hack-apollo/hack_clock/hardware/images/2.jpg

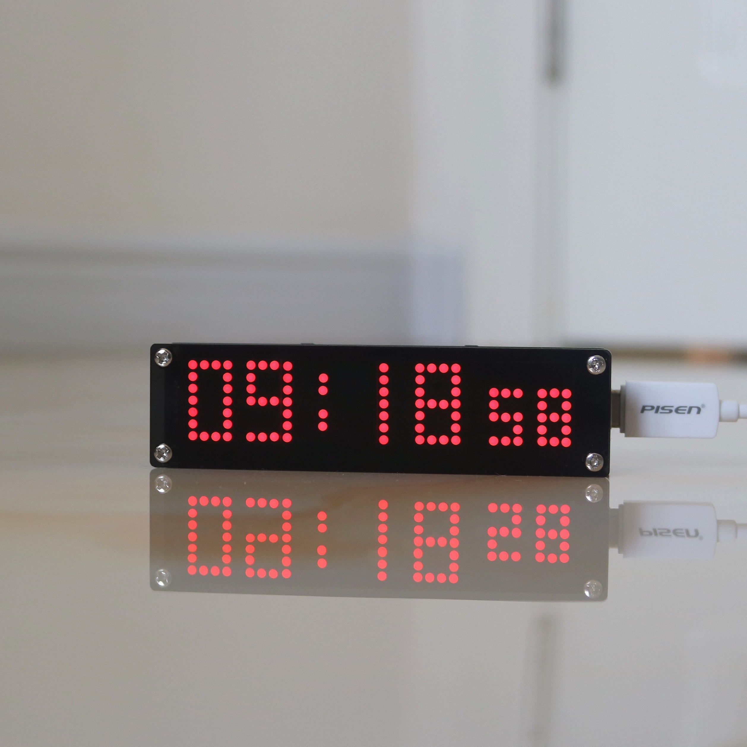
hardware/images/2.jpg
