hack-apollo/hack_clock/hardware/images/3.JPG

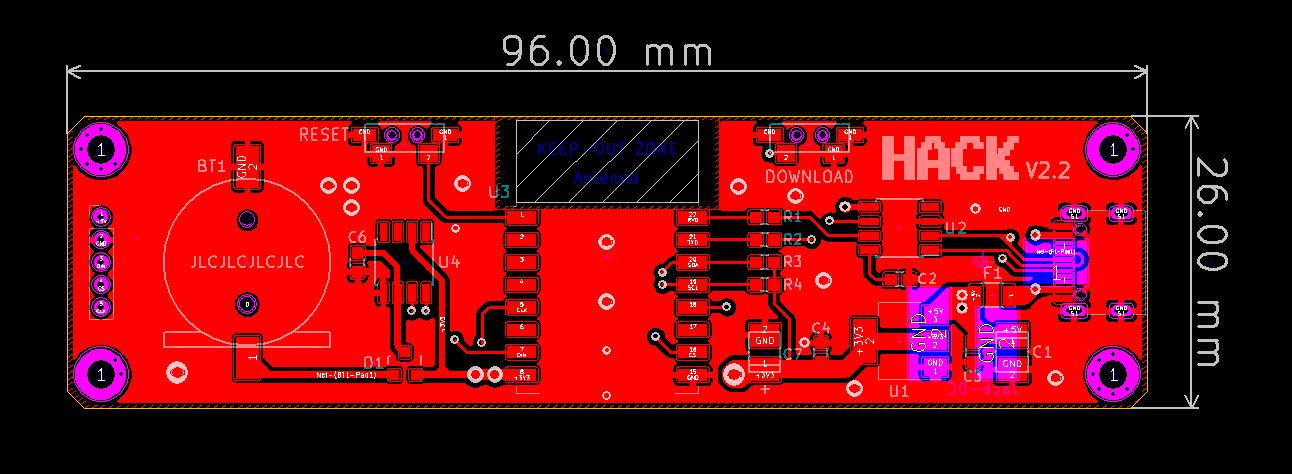
hardware/images/3.JPG
